TurtleCrawler/Mercury-One.1---Metal-Stepper-Mounts/Metric/RevB standard inserts/Printed Bottom Left Insert.stl

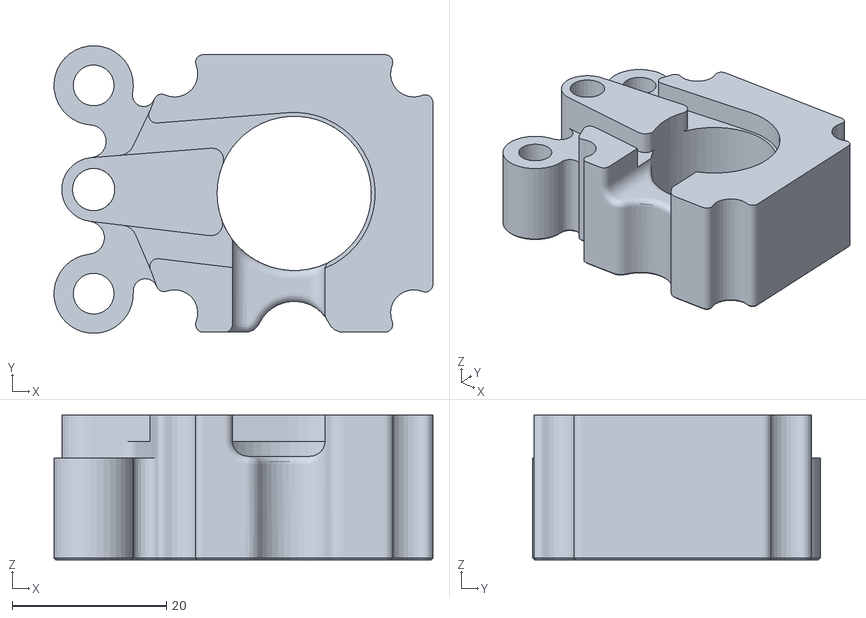
[picture p18: CAD file, 2024-08-05]
Metric/RevB standard inserts/Printed Bottom Left Insert.stl
49.1 x 37.3 x 18.8
