TurtleCrawler/Mercury-One.1---Metal-Stepper-Mounts/Imperial/RevB standard inserts/Printed Bottom Right Insert.stl

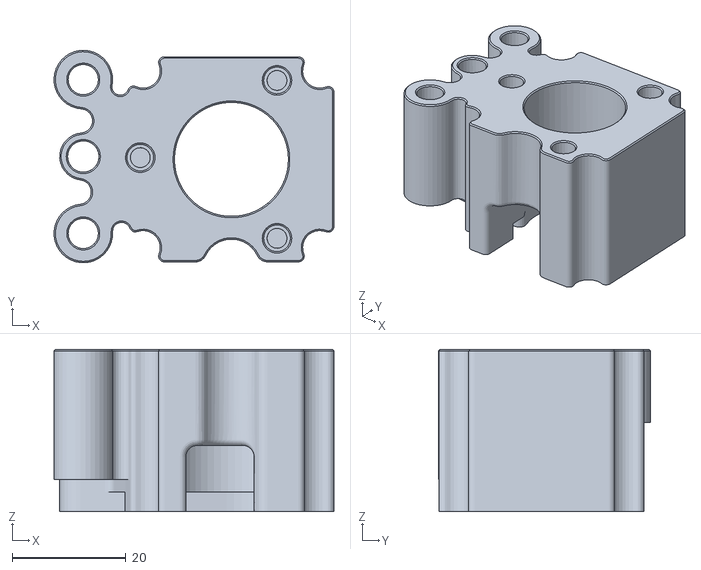
[picture p19: CAD file, 2024-08-05]
Imperial/RevB standard inserts/Printed Bottom Right Insert.stl
49.1 x 37.3 x 28.4
