TurtleCrawler/Mercury-One.1---Metal-Stepper-Mounts/Metric/RevB 0.2mm Offset Inserts/Printed Bottom Left Insert.stl

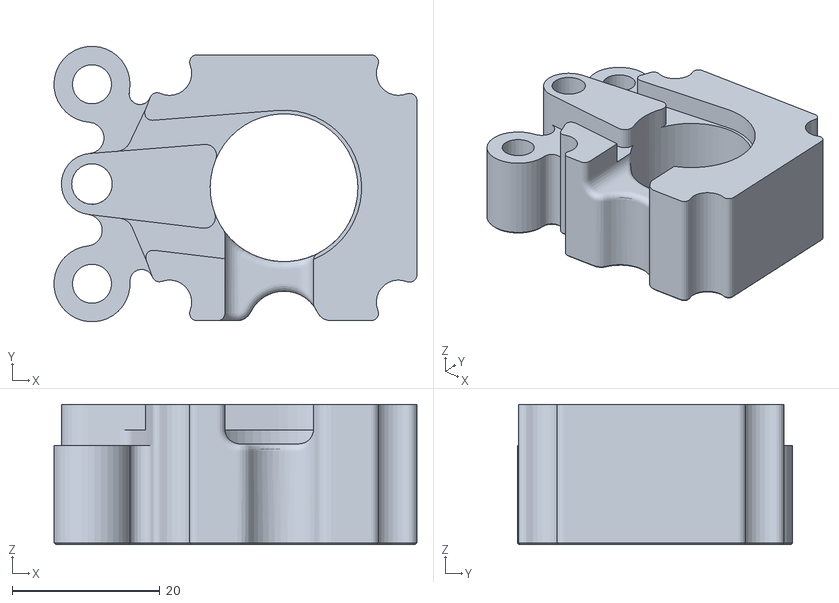
[picture p20: CAD file, 2024-08-05]
Metric/RevB 0.2mm Offset Inserts/Printed Bottom Left Insert.stl
49.1 x 37.3 x 19.0
